PatternAgents/Videre/Videre/eagleUp/eagleUp_Videre_board_bottom.jpg

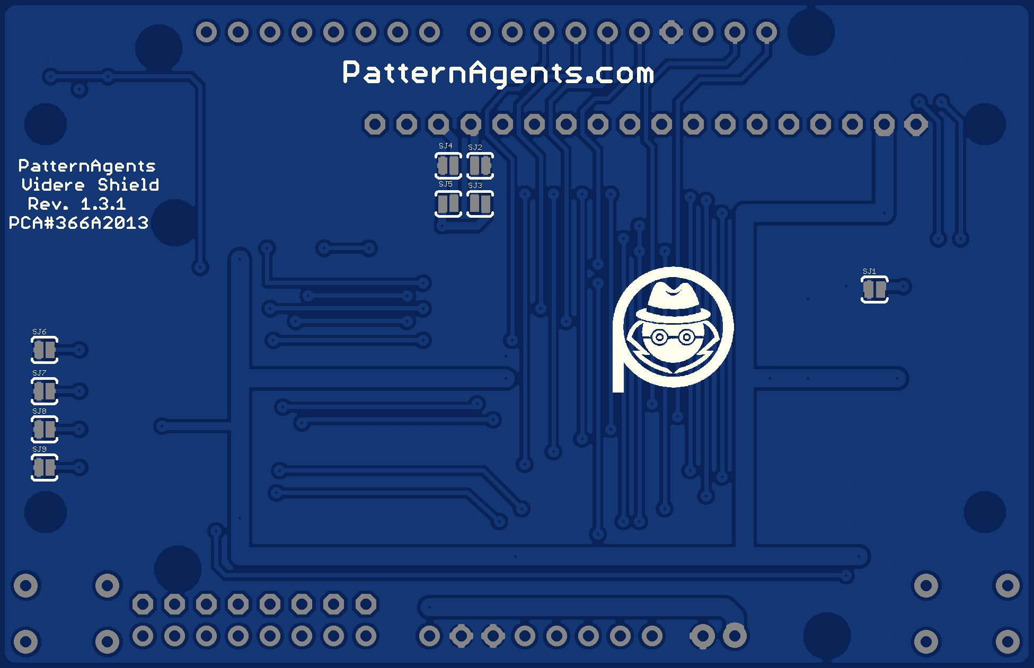
Videre/eagleUp/eagleUp_Videre_board_bottom.jpg
