PatternAgents/Videre/Videre/eagleUp/eagleUp_Videre_board_top.jpg

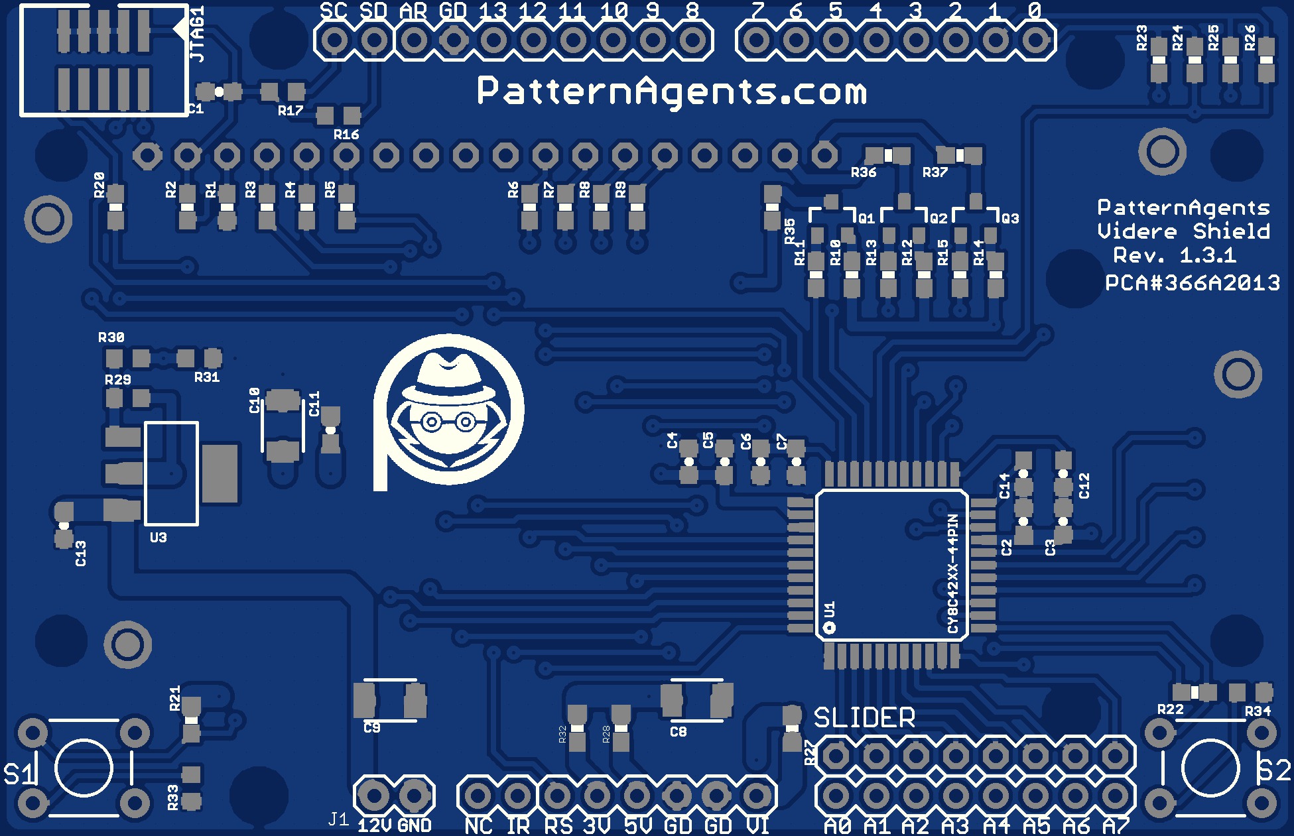
Videre/eagleUp/eagleUp_Videre_board_top.jpg
