PatternAgents/Videre/Videre/eagleUp/eagleUp_Videre_bottom.png

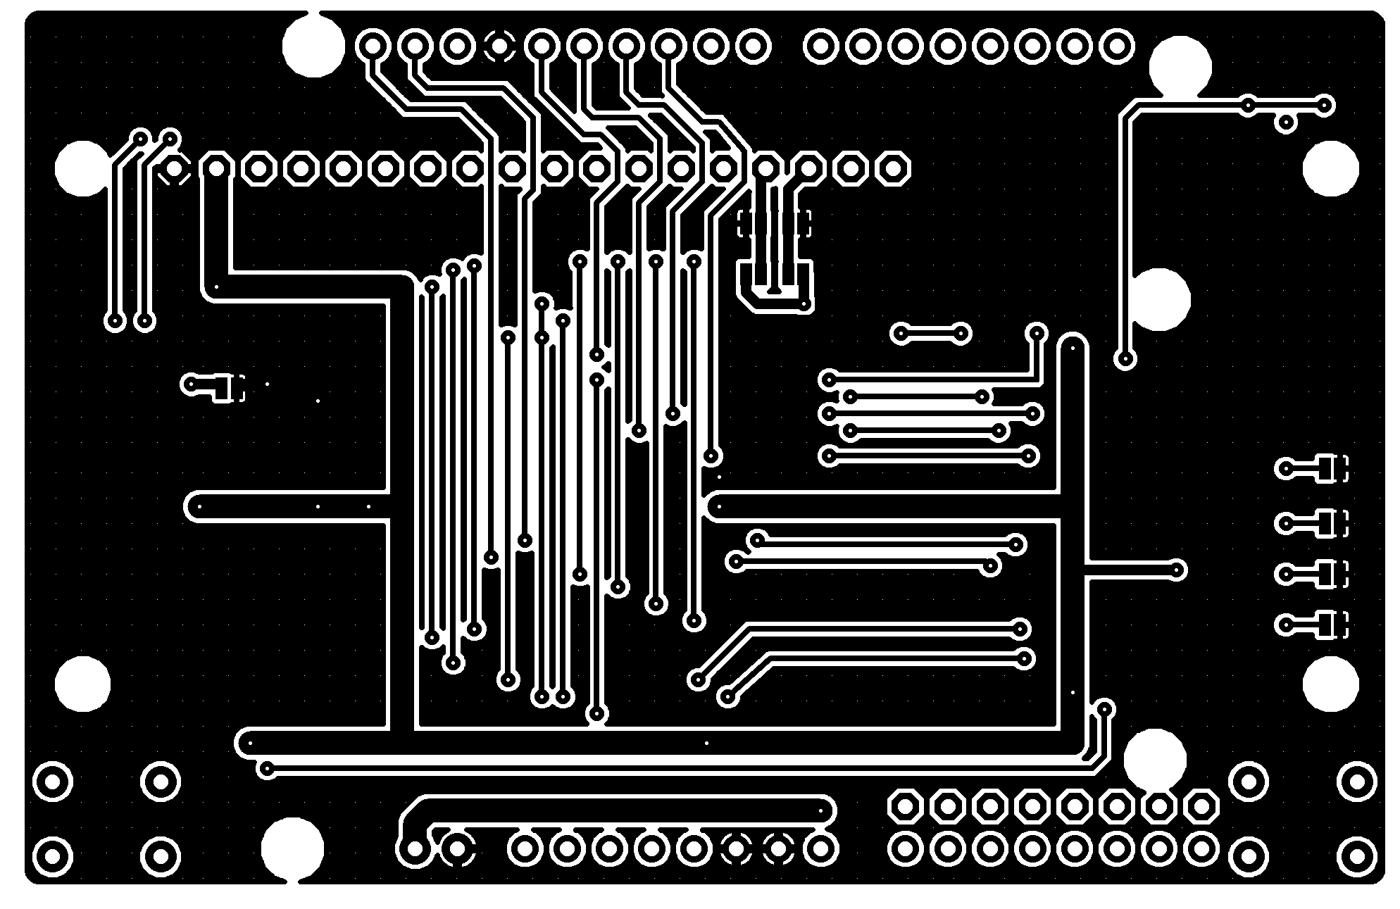
Videre/eagleUp/eagleUp_Videre_bottom.png
