PatternAgents/Videre/Videre/eagleUp/eagleUp_Videre_bottom_mask.png

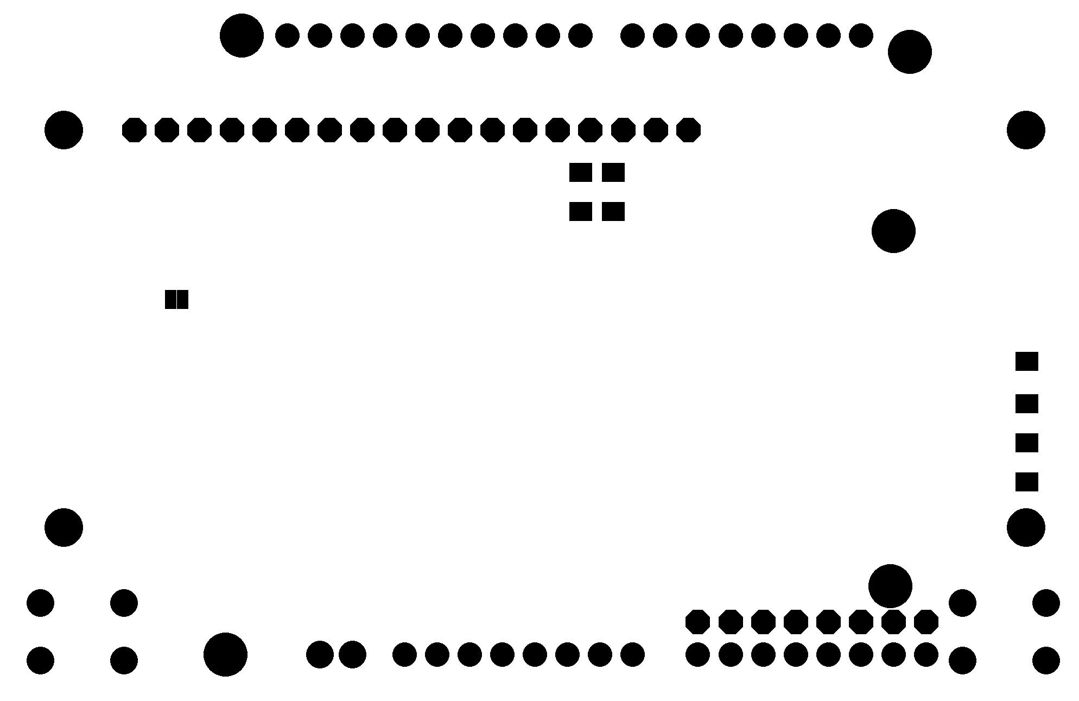
Videre/eagleUp/eagleUp_Videre_bottom_mask.png
