PatternAgents/Videre/Videre/eagleUp/eagleUp_Videre_bottom_silk.png

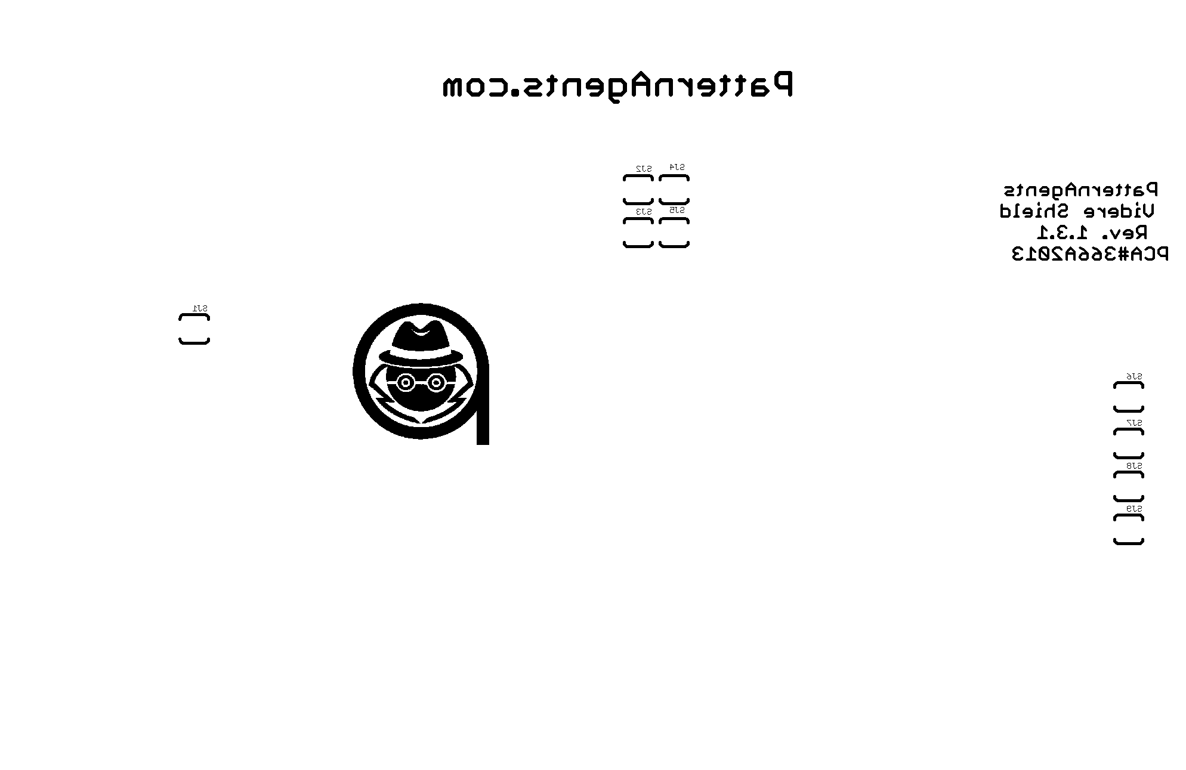
Videre/eagleUp/eagleUp_Videre_bottom_silk.png
