PatternAgents/Videre/Videre/eagleUp/eagleUp_Videre_imagesize.png

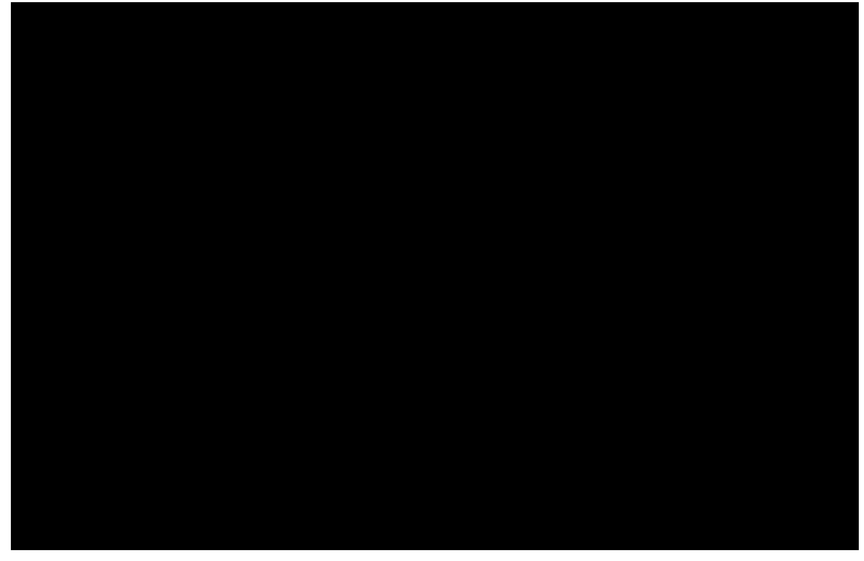
Videre/eagleUp/eagleUp_Videre_imagesize.png
