PatternAgents/Videre/Videre/eagleUp/eagleUp_Videre_outline.png

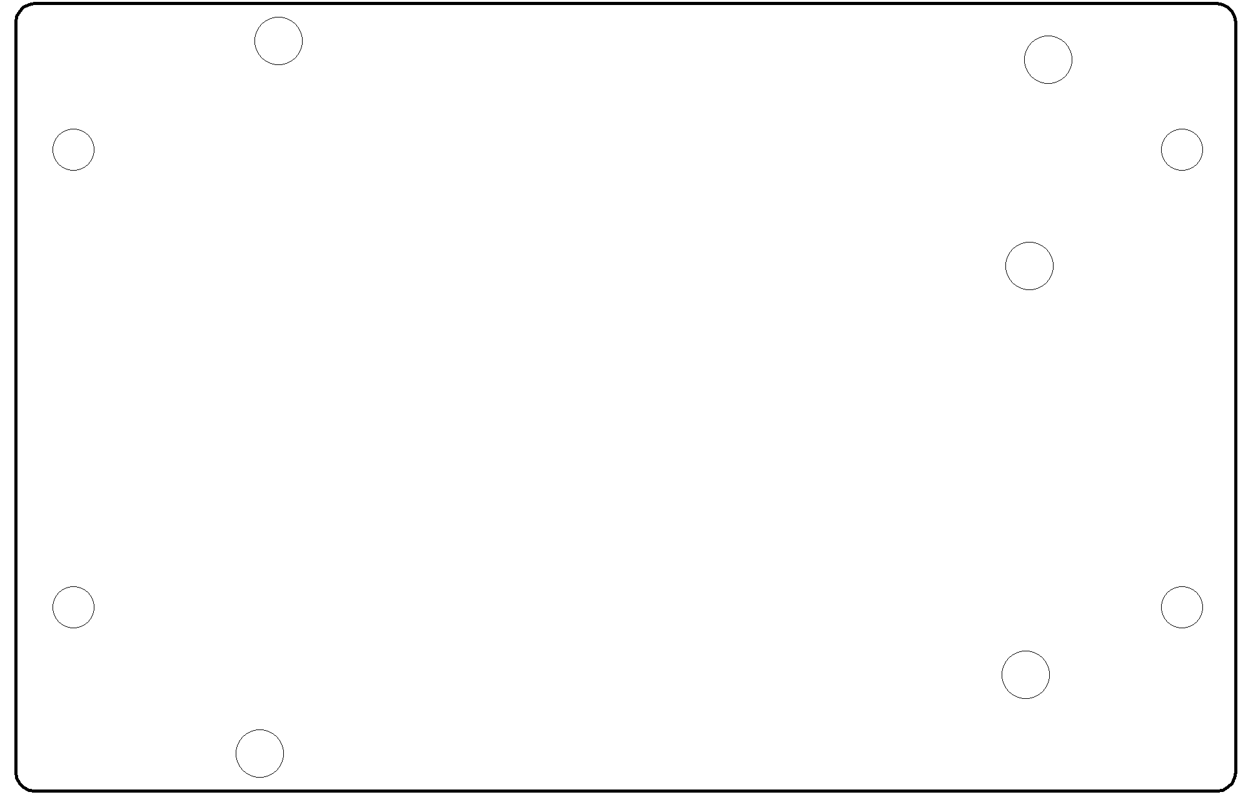
Videre/eagleUp/eagleUp_Videre_outline.png
