PatternAgents/Videre/Videre/eagleUp/eagleUp_Videre_top.png

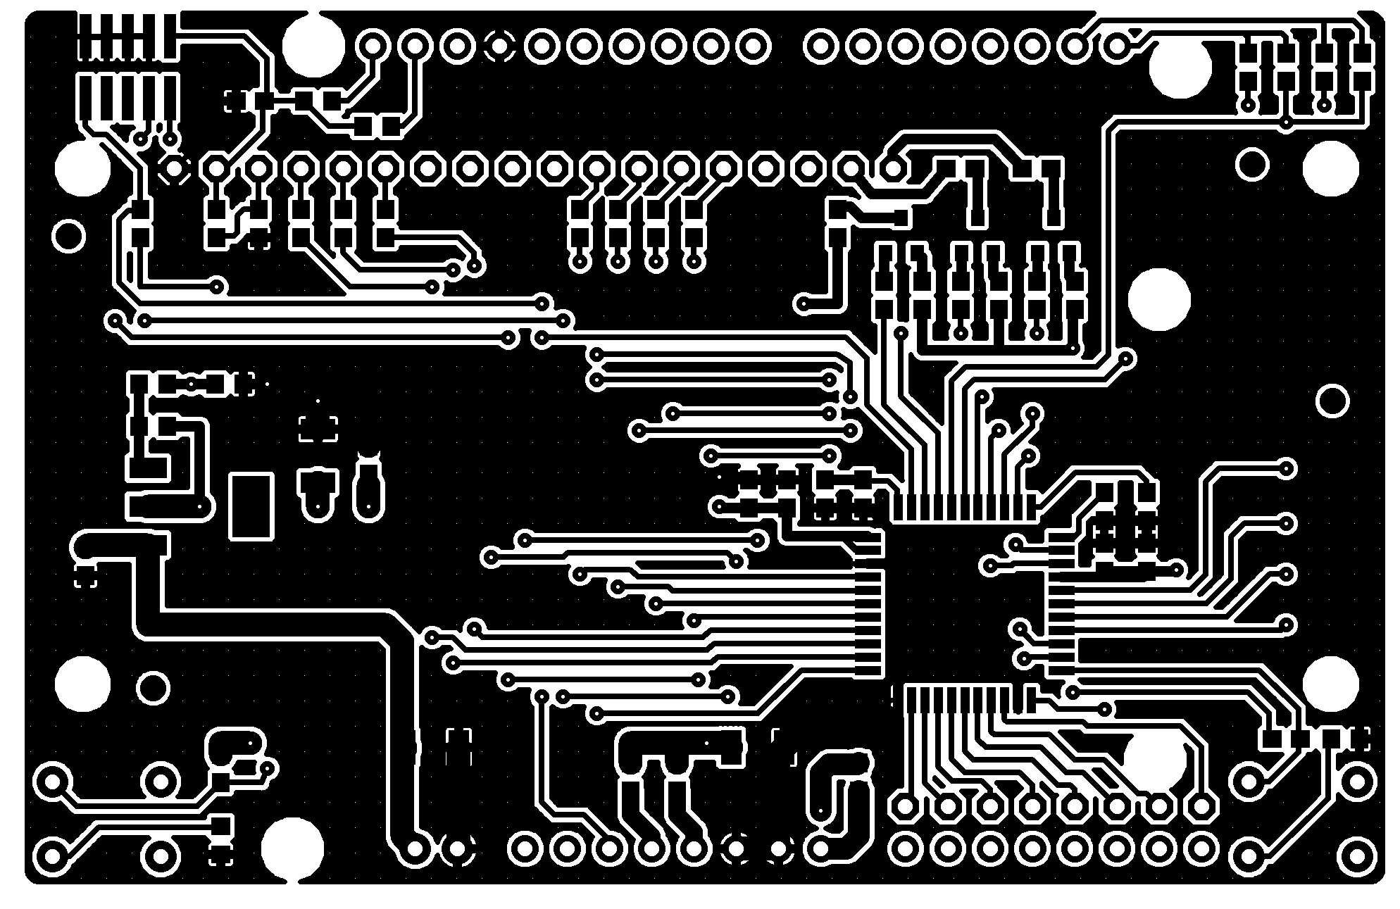
Videre/eagleUp/eagleUp_Videre_top.png
