PatternAgents/Videre/Videre/eagleUp/eagleUp_Videre_top_silk.png

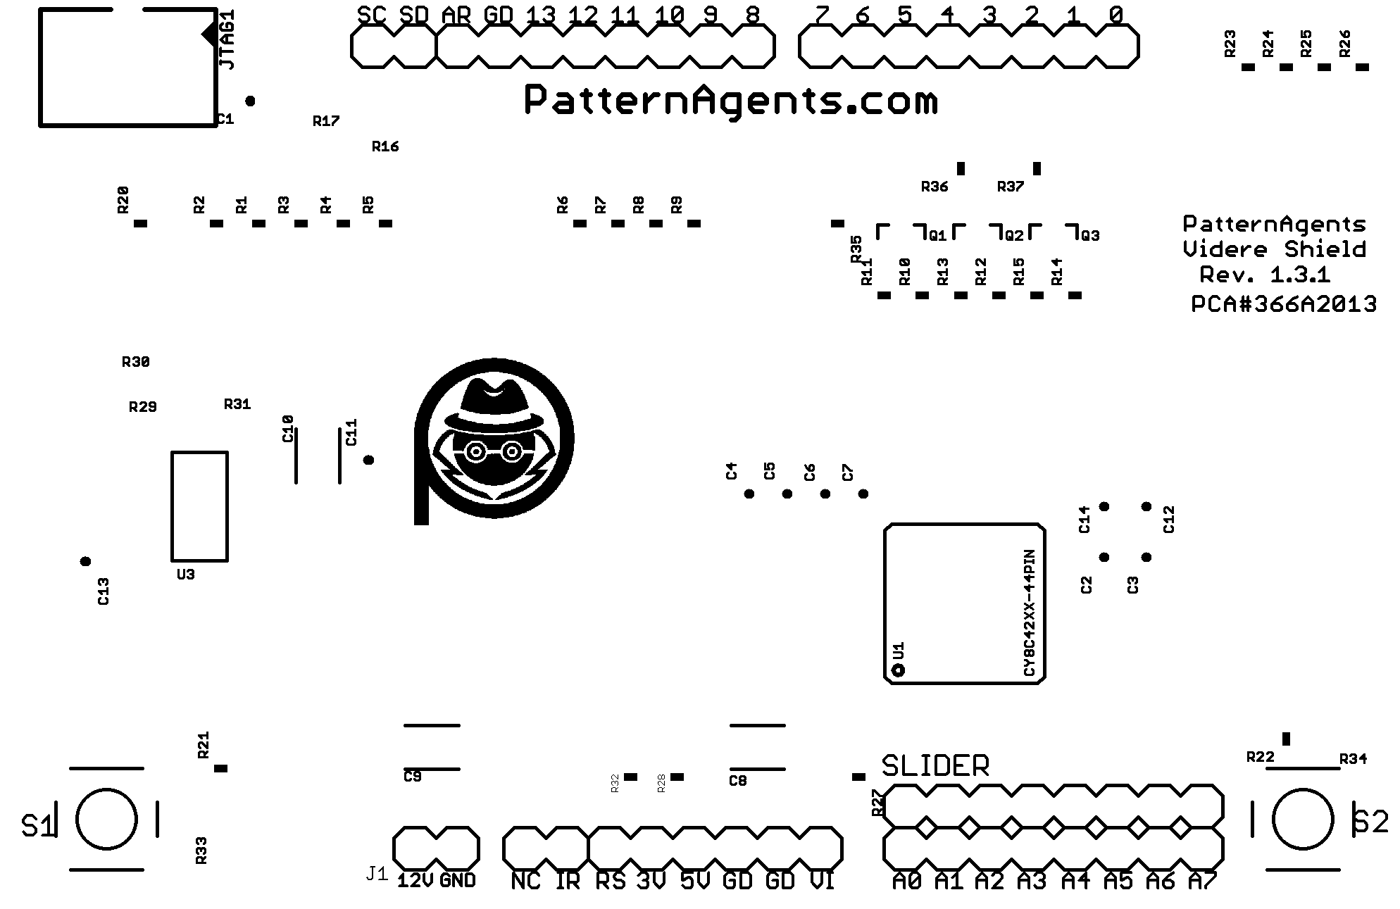
Videre/eagleUp/eagleUp_Videre_top_silk.png
